robinsonb5-PRs/icepi-zero/gallery/acron-on-icepi.jpg

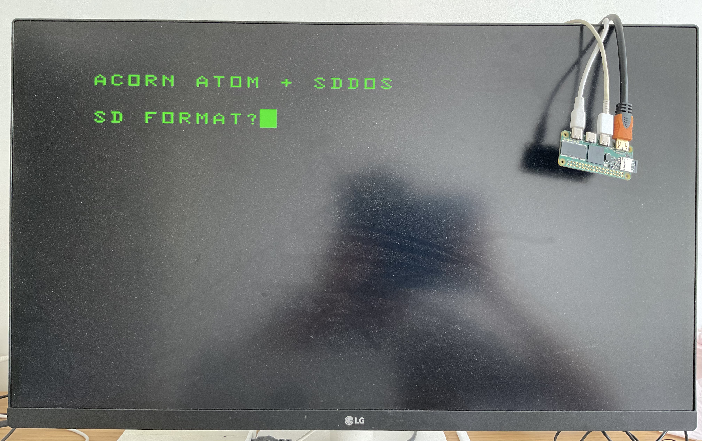
gallery/acron-on-icepi.jpg
