robinsonb5-PRs/icepi-zero/gallery/commodore-64-on-icepi.jpg

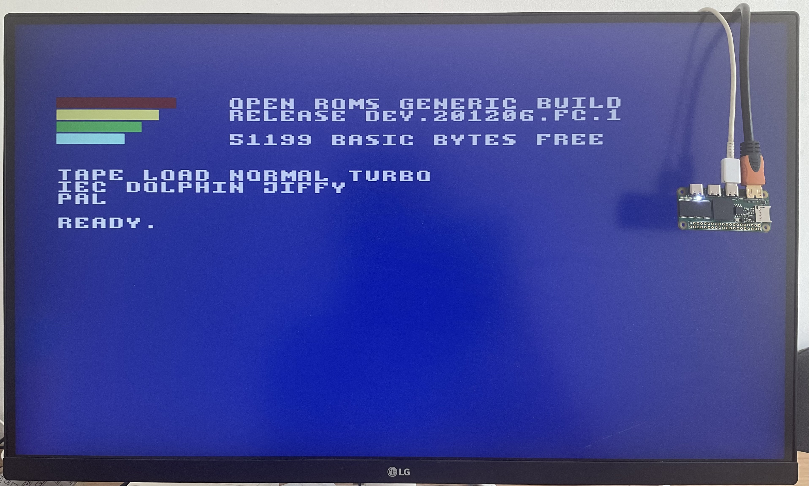
gallery/commodore-64-on-icepi.jpg
