robinsonb5-PRs/icepi-zero/gallery/icestudio-editor-ui.jpg

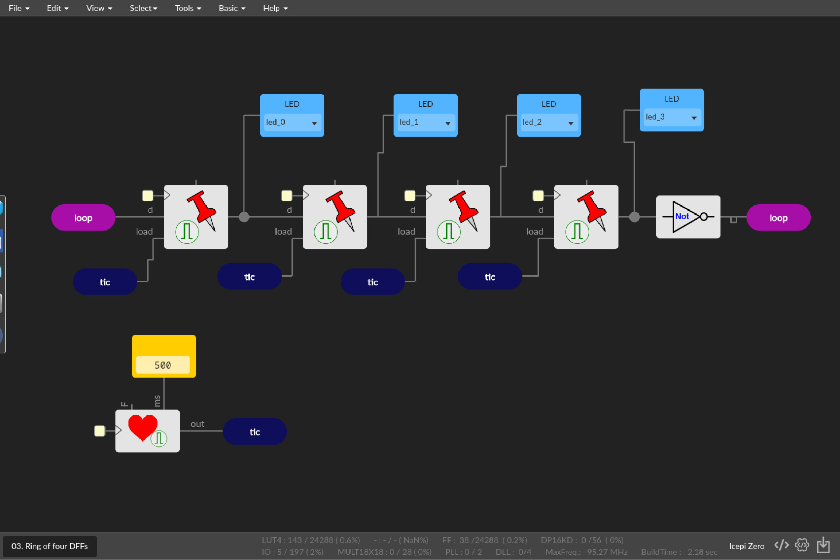
gallery/icestudio-editor-ui.jpg
