robinsonb5-PRs/icepi-zero/firmware/usb/report/top.sv

//
// Example using the usb_hid_host core, for the ULX3S board
// devietti, 11/2024
//

module top (
    input  clk,

    // UART output over US1 USB port
    output usb_tx,

    // LEDs
    output [4:0] led,

    // US2 USB port
    output [1:0] usb_pull_dp,
    output [1:0] usb_pull_dn,
    inout  [1:0] usb_dp,
    inout  [1:0] usb_dn
);
    assign usb_pull_dp = 2'b0;
    assign usb_pull_dn = 2'b0;

    wire sys_resetn;
    wire clk_usb;
    wire [1:0] usb_type;
    wire [7:0] key_modifiers, key1, key2, key3, key4;
    wire [7:0] mouse_btn;
    wire signed [7:0] mouse_dx, mouse_dy;
    wire [63:0] hid_report;
    wire usb_report, usb_conerr, game_l, game_r, game_u, game_d, game_a, game_b, game_x, game_y;
    wire game_sel, game_sta;

    pll_usb pll_usb(
        .clk(clk),
        .clkout0(),
        .clkout1(clk_usb),       // 12Mhz usb clock
        .locked(sys_resetn)
    );

    usb_hid_host usb (
        .usbclk(clk_usb), .usbrst_n(sys_resetn),
        .usb_dm(usb_dn[0]), .usb_dp(usb_dp[0]),
        .typ(usb_type), .report(usb_report),
        .key_modifiers(key_modifiers), .key1(key1), .key2(key2), .key3(key3), .key4(key4),
        .mouse_btn(mouse_btn), .mouse_dx(mouse_dx), .mouse_dy(mouse_dy),
        .game_l(game_l), .game_r(game_r), .game_u(game_u), .game_d(game_d),
        .game_a(game_a), .game_b(game_b), .game_x(game_x), .game_y(game_y), 
        .game_sel(game_sel), .game_sta(game_sta),
        .conerr(usb_conerr), .dbg_hid_report(hid_report)
    );

    /*
    hid_printer prt (
        .clk(clk_usb), .resetn(sys_resetn),
        .uart_tx(usb_tx), .usb_type(usb_type), .usb_report(usb_report),
        .key_modifiers(key_modifiers), .key1(key1), .key2(key2), .key3(key3), .key4(key4),
        .mouse_btn(mouse_btn), .mouse_dx(mouse_dx), .mouse_dy(mouse_dy),
        .game_l(game_l), .game_r(game_r), .game_u(game_u), .game_d(game_d),
        .game_a(game_a), .game_b(game_b), .game_x(game_x), .game_y(game_y), 
        .game_sel(game_sel), .game_sta(game_sta)
    );
    */

    logic report_toggle;      // blinks whenever there's a report
    always_ff @(posedge clk_usb) if (usb_report) report_toggle <= ~report_toggle;

    assign led[0] = report_toggle;
    assign led[2:1] = usb_type;
    assign led[3] = |mouse_btn;
    assign led[4] = |key1;
endmodule
