robinsonb5-PRs/icepi-zero/firmware/uart/uart.sv

module top(
	input        clk,
	input        usb_rx,

	output       usb_tx,
	output [2:0] led
);
	logic       finish;
	logic [7:0] data;

	uart_tx TX (clk, finish, data, usb_tx);
	uart_rx RX (clk, usb_rx, finish, data);

	// Indicator leds
	assign led[0] = finish;
	assign led[1] = ~usb_rx;
	assign led[2] = ~usb_tx;
endmodule
