robinsonb5-PRs/icepi-zero/firmware/ps2/uart2ps2/uart_rx.sv

module uart_rx #(
	parameter CLK = 50000000,
	parameter BAUD_RATE = 115200,
	parameter BITS = 8
) (
    // TODO: Stop uart on buffer full
	input clk,
    input reset,
	input rx,

	output logic            finish,
	output logic [BITS-1:0] data
);
	localparam CLK_DIVISOR = CLK / BAUD_RATE;

	logic [$clog2(CLK_DIVISOR):0] clkd;
	logic [$clog2(BITS)-1:0]      index;

	enum {IDLE, START, TRANSMISSION, STOP} state;

	always_ff @(posedge clk) begin
        if (reset) begin
            finish = 0;
            data = 0;

            clkd = 0;
            index = 0;

            state = IDLE;
        end else begin
		case (state)
		IDLE: begin
			clkd <= 0;
			index <= 0;
			finish <= 1'b0;

			if (rx == 1'b0) begin
				state <= START;
			end
		end
		START: begin
			// Test at middle of clk cycle
			if (clkd == (CLK_DIVISOR-1)/2) begin
				clkd <= 0;

				if (rx == 1'b0) begin
					state <= TRANSMISSION;
				end else begin
					state <= IDLE;
				end
			end else begin
				clkd <= clkd + 1;
			end
		end
		TRANSMISSION: begin
			if (clkd < CLK_DIVISOR-1) begin
				clkd <= clkd + 1;
			end else begin
				clkd <= 0;
				data[index] <= rx;

				if (index < (BITS-1)) begin
					// Transmit a bit
					index <= index + 1;
				end else begin
					index <= 0;
					state <= STOP;
				end
			end
		end
		STOP: begin
			finish <= 1'b1;

			if (clkd < CLK_DIVISOR-1) begin
				clkd <= clkd + 1;
			end else begin
				clkd <= 0;
				state <= IDLE;
			end
		end
		endcase
        end
	end
endmodule
